Sakuhano/Tatacon/schematic/tntebox.kicad_sch

## KiCad design schematic/tntebox.kicad_sch (2026-06-20)

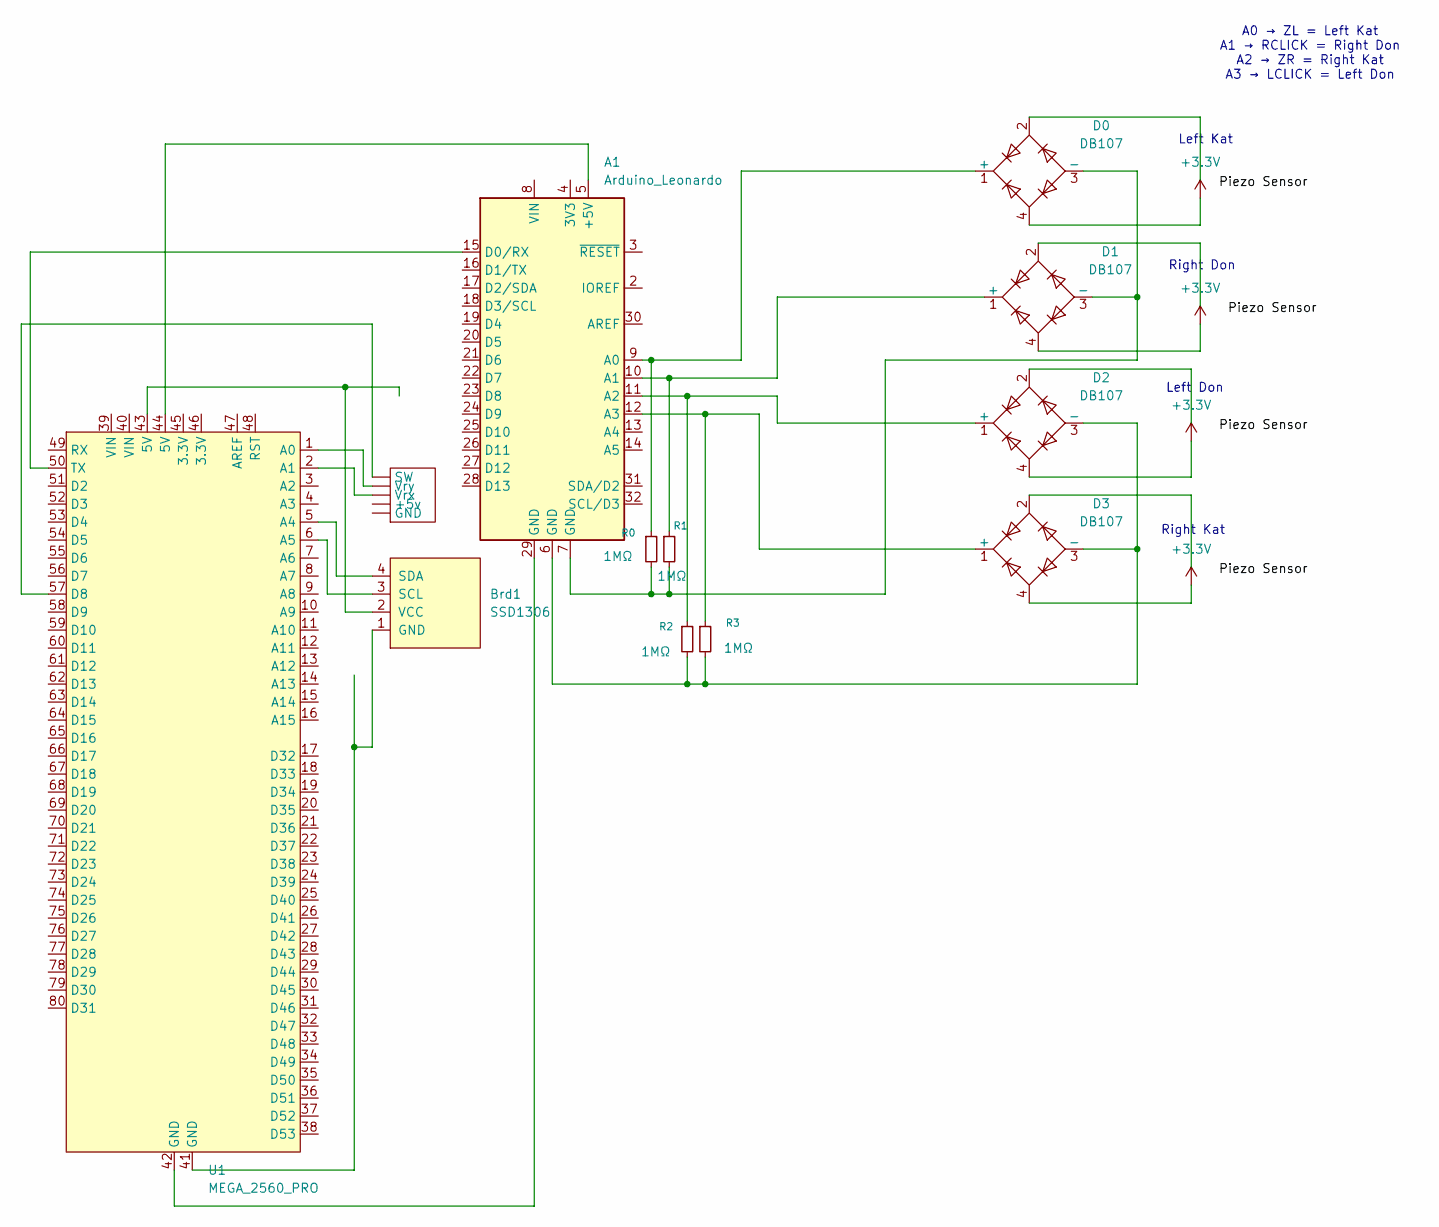
[picture p25: schematic tntebox.kicad_sch]

Parts:
A1: Arduino_Leonardo; Arduino_UNO_R3
Brd1: SSD1306
D0, D1, D2, D3: DB107; Diode_Bridge_Round_D9.8mm
R0, R1, R2, R3: 1MΩ
U1: MEGA_2560_PRO; mega2560pro
U2: (no value)

Connections:
+3.3V: D0.4, D1.4, D2.4, D3.4
unnamed: A1.5 (+5V), U1.44 (5V)
unnamed: A1.6 (GND), D2.3 (-), D3.3 (-), R2.2, R3.2
unnamed: A1.7 (GND), D0.3 (-), D1.3 (-), R0.2, R1.2
unnamed: A1.9 (A0), D0.1 (+), R0.1
unnamed: A1.10 (A1), D1.1 (+), R1.1
unnamed: A1.11 (A2), D2.1 (+), R2.1
unnamed: A1.12 (A3), D3.1 (+), R3.1
unnamed: A1.15 (D0/RX), U1.50 (TX)
unnamed: A1.29 (GND), U1.42 (GND)
unnamed: Brd1.1 (GND), U1.41 (GND)
unnamed: Brd1.2 (VCC), U1.43 (5V)
unnamed: Brd1.3 (SCL), U1.6 (A5)
unnamed: Brd1.4 (SDA), U1.5 (A4)
unnamed: U1.1 (A0), U2.
unnamed: U1.2 (A1), U2.
unnamed: U1.57 (D8), U2.

Notes on the sheet:
Right Don
Right Kat
Left Kat
Left Don
A0 → ZL = Left Kat A1 → RCLICK = Right Don A2 → ZR = Right Kat A3 → LCLICK = Left Don
